mcounter/BatteryCounter/micro/BattRX/UserInterfaceLang.h

#ifndef __USERINTERFACELANG_H_
#define __USERINTERFACELANG_H_

#define USER_TEXT_CONST_EMPTY                                           (0)
#define USER_TEXT_CONST_MESSAGE_DONE                                    (1)
#define USER_TEXT_CONST_MESSAGE_ERROR                                   (2)
#define USER_TEXT_CONST_MESSAGE_SAVING                                  (3)
#define USER_TEXT_CONST_SWITCH_OFF                                      (4)
#define USER_TEXT_CONST_SWITCH_ON                                       (5)
#define USER_TEXT_CONST_SWITCH_NO                                       (6)
#define USER_TEXT_CONST_SWITCH_YES                                      (7)
#define USER_TEXT_CONST_MENU_REPORTS                                    (8)
#define USER_TEXT_CONST_MENU_SETUP                                      (9)
#define USER_TEXT_CONST_MENU_MAINTENANCE                                (10)
#define USER_TEXT_CONST_MENU_INFO                                       (11)
#define USER_TEXT_CONST_SETUP_CLOCK                                     (12)
#define USER_TEXT_CONST_SETUP_SUMMERTIME_L1                             (13)
#define USER_TEXT_CONST_SETUP_SUMMERTIME_L2                             (14)
#define USER_TEXT_CONST_SETUP_SUMMERTIME_AUTO                           (15)
#define USER_TEXT_CONST_SETUP_SUMMERTIME_UKR                            (16)
#define USER_TEXT_CONST_SETUP_COUNTER_L1                                (17)
#define USER_TEXT_CONST_SETUP_COUNTER_L2                                (18)
#define USER_TEXT_CONST_SETUP_COUNTER_DETECTOR_L1                       (19)
#define USER_TEXT_CONST_SETUP_COUNTER_DETECTOR_L2                       (20)
#define USER_TEXT_CONST_SETUP_COUNTER_DETECTOR_NODETECTION              (21)
#define USER_TEXT_CONST_SETUP_COUNTER_DETECTOR_NODETECTIONDIV2          (22)
#define USER_TEXT_CONST_SETUP_COUNTER_DETECTOR_SIMULATION               (23)
#define USER_TEXT_CONST_SETUP_COUNTER_DETECTOR_STRONGDETECTION          (24)
#define USER_TEXT_CONST_SETUP_COUNTER_DETECTOR_SOFTDETECTION            (25)
#define USER_TEXT_CONST_SETUP_COUNTER_INVERTCOUNT_L1                    (26)
#define USER_TEXT_CONST_SETUP_COUNTER_INVERTCOUNT_L2                    (27)
#define USER_TEXT_CONST_SETUP_COUNTER_DETECTIONTIME                     (28)
#define USER_TEXT_CONST_SETUP_ENERGYSAVING_L1                           (29)
#define USER_TEXT_CONST_SETUP_ENERGYSAVING_L2                           (30)
#define USER_TEXT_CONST_SETUP_ENERGYSAVING_SAVEMODE_L1                  (31)
#define USER_TEXT_CONST_SETUP_ENERGYSAVING_SAVEMODE_L2                  (32)
#define USER_TEXT_CONST_SETUP_ENERGYSAVING_SAVEMODE_MIN                 (33)
#define USER_TEXT_CONST_SETUP_ENERGYSAVING_SAVEMODE_NOCOUNT_L1          (34)
#define USER_TEXT_CONST_SETUP_ENERGYSAVING_SAVEMODE_NOCOUNT_L2          (35)
#define USER_TEXT_CONST_SETUP_ENERGYSAVING_SAVEMODE_NOSCREEN_L1         (36)
#define USER_TEXT_CONST_SETUP_ENERGYSAVING_SAVEMODE_NOSCREEN_L2         (37)
#define USER_TEXT_CONST_SETUP_ENERGYSAVING_SAVEMODE_MAX                 (38)
#define USER_TEXT_CONST_SETUP_ENERGYSAVING_INACTIVITYTIME_L1            (39)
#define USER_TEXT_CONST_SETUP_ENERGYSAVING_INACTIVITYTIME_L2            (40)
#define USER_TEXT_CONST_SETUP_ENERGYSAVING_WORKWEEK_L1                  (41)
#define USER_TEXT_CONST_SETUP_ENERGYSAVING_WORKWEEK_L2                  (42)
#define USER_TEXT_CONST_SETUP_ENERGYSAVING_WORKWEEK_MASK                (43)
#define USER_TEXT_CONST_SETUP_ENERGYSAVING_WORKTODAY_L1                 (44)
#define USER_TEXT_CONST_SETUP_ENERGYSAVING_WORKTODAY_L2                 (45)
#define USER_TEXT_CONST_SETUP_ENERGYSAVING_WORKDAY_L1                   (46)
#define USER_TEXT_CONST_SETUP_ENERGYSAVING_WORKDAY_L2                   (47)
#define USER_TEXT_CONST_SETUP_ENERGYSAVING_WORKDAY_24H                  (48)
#define USER_TEXT_CONST_SETUP_ENERGYSAVING_WORKDAY_1SHIFT               (49)
#define USER_TEXT_CONST_SETUP_ENERGYSAVING_WORKDAY_2SHIFTS              (50)
#define USER_TEXT_CONST_SETUP_ENERGYSAVING_WORKDAY_WITHLUNCH            (51)
#define USER_TEXT_CONST_SETUP_PASSWORD                                  (52)
#define USER_TEXT_CONST_SETUP_PASSWORD_MASTER                           (53)
#define USER_TEXT_CONST_SETUP_PASSWORD_MANAGER                          (54)
#define USER_TEXT_CONST_SETUP_PASSWORD_CURRENT                          (55)
#define USER_TEXT_CONST_SETUP_PASSWORD_NEW                              (56)
#define USER_TEXT_CONST_SETUP_PASSWORD_REPEAT                           (57)
#define USER_TEXT_CONST_SETUP_INTERFACE                                 (58)
#define USER_TEXT_CONST_MAINTENANCE_RESET_COUNTERS_L1                   (59)
#define USER_TEXT_CONST_MAINTENANCE_RESET_COUNTERS_L2                   (60)
#define USER_TEXT_CONST_MAINTENANCE_RESET_FACTORY_L1                    (61)
#define USER_TEXT_CONST_MAINTENANCE_RESET_FACTORY_L2                    (62)
#define USER_TEXT_CONST_MAINTENANCE_RESET_DATA                          (63)
#define USER_TEXT_CONST_MAINTENANCE_RESET_FULL                          (64)
#define USER_TEXT_CONST_MAINTENANCE_SAFE_BATT_REMOVE_L1                 (65)
#define USER_TEXT_CONST_MAINTENANCE_SAFE_BATT_REMOVE_L2                 (66)
#define USER_TEXT_CONST_REPORTS_VISITORS                                (67)
#define USER_TEXT_CONST_REPORTS_TOTAL                                   (68)
#define USER_TEXT_CONST_REPORTS_HOUR                                    (69)
#define USER_TEXT_CONST_REPORTS_DAY                                     (70)
#define USER_TEXT_CONST_REPORTS_WEEK                                    (71)
#define USER_TEXT_CONST_REPORTS_MONTH                                   (72)
#define USER_TEXT_CONST_REPORTS_NOSENSOR                                (73)
#define USER_TEXT_CONST_REPORTS_MESSAGE_INCNT                           (74)
#define USER_TEXT_CONST_REPORTS_MESSAGE_OUTCNT                          (75)
#define USER_TEXT_CONST_REPORTS_MESSAGE_TOTALCNT                        (76)
#define USER_TEXT_CONST_REPORTS_MESSAGE_INCNT_SHORT                     (77)
#define USER_TEXT_CONST_REPORTS_MESSAGE_OUTCNT_SHORT                    (78)
#define USER_TEXT_CONST_MONTH_NAME_JANUARY                              (79)
#define USER_TEXT_CONST_MONTH_NAME_FEBRUARY                             (80)
#define USER_TEXT_CONST_MONTH_NAME_MARCH                                (81)
#define USER_TEXT_CONST_MONTH_NAME_APRIL                                (82)
#define USER_TEXT_CONST_MONTH_NAME_MAY                                  (83)
#define USER_TEXT_CONST_MONTH_NAME_JUNE                                 (84)
#define USER_TEXT_CONST_MONTH_NAME_JULY                                 (85)
#define USER_TEXT_CONST_MONTH_NAME_AUGUST                               (86)
#define USER_TEXT_CONST_MONTH_NAME_SEPTEMBER                            (87)
#define USER_TEXT_CONST_MONTH_NAME_OCTOBER                              (88)
#define USER_TEXT_CONST_MONTH_NAME_NOVEMBER                             (89)
#define USER_TEXT_CONST_MONTH_NAME_DECEMBER                             (90)
#define USER_TEXT_CONST_TEXT_MILLISECONDS_SHORT                         (91)
#define USER_TEXT_CONST_TEXT_SECONDS_SHORT                              (92)
#define USER_TEXT_CONST_TEXT_TIMEOUT                                    (93)
#define USER_TEXT_CONST_TEXT_SHIFT1                                     (94)
#define USER_TEXT_CONST_TEXT_SHIFT2                                     (95)
#define USER_TEXT_CONST_TEXT_LUNCH                                      (96)
#define USER_TEXT_CONST_MESSAGE_TYPE_PASSWORD                           (97)
#define USER_TEXT_CONST_TEXT_WIDGET_COUNT_IN                            (98)
#define USER_TEXT_CONST_TEXT_WIDGET_COUNT_OUT                           (99)
#define USER_TEXT_CONST_TEXT_WIDGET_COUNT_AVG                           (100)
#define USER_TEXT_CONST_TEXT_WIDGET_COUNT_MAX                           (101)
#define USER_TEXT_CONST_TEXT_WIDGET_COUNT_MIN                           (102)
#define USER_TEXT_CONST_TEXT_WIDGET_NOSENSOR                            (103)
#define USER_TEXT_CONST_TEXT_WIDGET_HOUR_SHORT                          (104)
#define USER_TEXT_CONST_TEXT_WIDGET_DAY_SHORT                           (105)
#define USER_TEXT_CONST_TEXT_WIDGET_WEEK_SHORT                          (106)
#define USER_TEXT_CONST_TEXT_WIDGET_MONTH_SHORT                         (107)
#define USER_TEXT_CONST_TEXT_WIDGET_TOTAL_SHORT                         (108)
#define USER_TEXT_CONST_INFO_RESETNUM_L1                                (109)
#define USER_TEXT_CONST_INFO_RESETNUM_L2                                (110)
#define USER_TEXT_CONST_INFO_RESETNUM_RESTARTS                          (111)
#define USER_TEXT_CONST_INFO_RESETNUM_DATARESET                         (112)
#define USER_TEXT_CONST_INFO_RESETNUM_FACTORYRESET                      (113)
#define USER_TEXT_CONST_INFO_RESETNUM_PASSWORDFAILS_L1                  (114)
#define USER_TEXT_CONST_INFO_RESETNUM_PASSWORDFAILS_L2                  (115)
#define USER_TEXT_CONST_INFO_SERIALNUM                                  (116)
#define USER_TEXT_CONST_INFO_BATTERY_VOLTAGE                            (117)
#define USER_TEXT_CONST_MAINTENANCE_SENSORQUALITY_L1                    (118)
#define USER_TEXT_CONST_MAINTENANCE_SENSORQUALITY_L2                    (119)
#define USER_TEXT_CONST_SETUP_ENERGYSAVING_BACKLIGHT                    (120)
#define USER_TEXT_CONST_SETUP_WIDGETS                                   (121)
#define USER_TEXT_CONST_SETUP_WIDGETS_L1                                (122)
#define USER_TEXT_CONST_SETUP_WIDGETS_MAIN                              (123)
#define USER_TEXT_CONST_SETUP_WIDGETS_LEFT                              (124)
#define USER_TEXT_CONST_SETUP_WIDGETS_RIGHT                             (125)
#define USER_TEXT_CONST_TEXT_WIDGET_SWITCHED_OFF                        (126)
#define USER_TEXT_CONST_TEXT_WIDGET_COUNTER1_SHORT                      (127)
#define USER_TEXT_CONST_TEXT_WIDGET_COUNTER2_SHORT                      (128)
#define USER_TEXT_CONST_TEXT_WIDGET_COUNTER1_LONG                       (129)
#define USER_TEXT_CONST_TEXT_WIDGET_COUNTER2_LONG                       (130)
#define USER_TEXT_CONST_TEXT_WIDGET_COUNTER_AGGREGATION_MODE            (131)
#define USER_TEXT_CONST_TEXT_WIDGET_COUNTER_AGGREGATION_IN              (132)
#define USER_TEXT_CONST_TEXT_WIDGET_COUNTER_AGGREGATION_OUT             (133)
#define USER_TEXT_CONST_TEXT_WIDGET_COUNTER_AGGREGATION_AVG             (134)
#define USER_TEXT_CONST_TEXT_WIDGET_COUNTER_AGGREGATION_MAX             (135)
#define USER_TEXT_CONST_TEXT_WIDGET_COUNTER_AGGREGATION_MIN             (136)
#define USER_TEXT_CONST_TEXT_WIDGET_COUNTER_SHIFT                       (137)
#define USER_TEXT_CONST_SETUP_SCREENSAVER                               (138)
#define USER_TEXT_CONST_SETUP_SCREENSAVER_OFF                           (139)
#define USER_TEXT_CONST_SETUP_SCREENSAVER_ON                            (140)

namespace UserInterface
{
  unsigned char __generic * getString(unsigned short _strId);
}
#endif
