mcounter/BatteryCounter/micro/BattRX/UserInterfaceLang_RUS.h

#ifndef __USERINTERFACELANG_RUS_H_
#define __USERINTERFACELANG_RUS_H_

namespace UserInterface
{
  __flash const unsigned short textReference_RUS[] =
  {
       0,         //USER_TEXT_CONST_EMPTY
       1,         //USER_TEXT_CONST_MESSAGE_DONE
      11,         //USER_TEXT_CONST_MESSAGE_ERROR
      18,         //USER_TEXT_CONST_MESSAGE_SAVING
      29,         //USER_TEXT_CONST_SWITCH_OFF
      39,         //USER_TEXT_CONST_SWITCH_ON
      48,         //USER_TEXT_CONST_SWITCH_NO
      52,         //USER_TEXT_CONST_SWITCH_YES
      55,         //USER_TEXT_CONST_MENU_REPORTS
      62,         //USER_TEXT_CONST_MENU_SETUP
      72,         //USER_TEXT_CONST_MENU_MAINTENANCE
      85,         //USER_TEXT_CONST_MENU_INFO
      96,         //USER_TEXT_CONST_SETUP_CLOCK
     109,         //USER_TEXT_CONST_SETUP_SUMMERTIME_L1
     116,         //USER_TEXT_CONST_SETUP_SUMMERTIME_L2
     122,         //USER_TEXT_CONST_SETUP_SUMMERTIME_AUTO
     136,         //USER_TEXT_CONST_SETUP_SUMMERTIME_UKR
     144,         //USER_TEXT_CONST_SETUP_COUNTER_L1
     152,         //USER_TEXT_CONST_SETUP_COUNTER_L2
     164,         //USER_TEXT_CONST_SETUP_COUNTER_DETECTOR_L1
     173,         //USER_TEXT_CONST_SETUP_COUNTER_DETECTOR_L2
     185,         //USER_TEXT_CONST_SETUP_COUNTER_DETECTOR_NODETECTION
     198,         //USER_TEXT_CONST_SETUP_COUNTER_DETECTOR_NODETECTIONDIV2
     210,         //USER_TEXT_CONST_SETUP_COUNTER_DETECTOR_SIMULATION
     219,         //USER_TEXT_CONST_SETUP_COUNTER_DETECTOR_STRONGDETECTION
     235,         //USER_TEXT_CONST_SETUP_COUNTER_DETECTOR_SOFTDETECTION
     251,         //USER_TEXT_CONST_SETUP_COUNTER_INVERTCOUNT_L1
     265,         //USER_TEXT_CONST_SETUP_COUNTER_INVERTCOUNT_L2
     270,         //USER_TEXT_CONST_SETUP_COUNTER_DETECTIONTIME
     285,         //USER_TEXT_CONST_SETUP_ENERGYSAVING_L1
     294,         //USER_TEXT_CONST_SETUP_ENERGYSAVING_L2
     302,         //USER_TEXT_CONST_SETUP_ENERGYSAVING_SAVEMODE_L1
     308,         //USER_TEXT_CONST_SETUP_ENERGYSAVING_SAVEMODE_L2
     317,         //USER_TEXT_CONST_SETUP_ENERGYSAVING_SAVEMODE_MIN
     325,         //USER_TEXT_CONST_SETUP_ENERGYSAVING_SAVEMODE_NOCOUNT_L1
     336,         //USER_TEXT_CONST_SETUP_ENERGYSAVING_SAVEMODE_NOCOUNT_L2
     343,         //USER_TEXT_CONST_SETUP_ENERGYSAVING_SAVEMODE_NOSCREEN_L1
     353,         //USER_TEXT_CONST_SETUP_ENERGYSAVING_SAVEMODE_NOSCREEN_L2
     359,         //USER_TEXT_CONST_SETUP_ENERGYSAVING_SAVEMODE_MAX
     368,         //USER_TEXT_CONST_SETUP_ENERGYSAVING_INACTIVITYTIME_L1
     375,         //USER_TEXT_CONST_SETUP_ENERGYSAVING_INACTIVITYTIME_L2
     387,         //USER_TEXT_CONST_SETUP_ENERGYSAVING_WORKWEEK_L1
     395,         //USER_TEXT_CONST_SETUP_ENERGYSAVING_WORKWEEK_L2
     402,         //USER_TEXT_CONST_SETUP_ENERGYSAVING_WORKWEEK_MASK
     416,         //USER_TEXT_CONST_SETUP_ENERGYSAVING_WORKTODAY_L1
     425,         //USER_TEXT_CONST_SETUP_ENERGYSAVING_WORKTODAY_L2
     433,         //USER_TEXT_CONST_SETUP_ENERGYSAVING_WORKDAY_L1
     441,         //USER_TEXT_CONST_SETUP_ENERGYSAVING_WORKDAY_L2
     446,         //USER_TEXT_CONST_SETUP_ENERGYSAVING_WORKDAY_24H
     454,         //USER_TEXT_CONST_SETUP_ENERGYSAVING_WORKDAY_1SHIFT
     462,         //USER_TEXT_CONST_SETUP_ENERGYSAVING_WORKDAY_2SHIFTS
     470,         //USER_TEXT_CONST_SETUP_ENERGYSAVING_WORKDAY_WITHLUNCH
     482,         //USER_TEXT_CONST_SETUP_PASSWORD
     489,         //USER_TEXT_CONST_SETUP_PASSWORD_MASTER
     504,         //USER_TEXT_CONST_SETUP_PASSWORD_MANAGER
     514,         //USER_TEXT_CONST_SETUP_PASSWORD_CURRENT
     529,         //USER_TEXT_CONST_SETUP_PASSWORD_NEW
     542,         //USER_TEXT_CONST_SETUP_PASSWORD_REPEAT
     552,         //USER_TEXT_CONST_SETUP_INTERFACE
     562,         //USER_TEXT_CONST_MAINTENANCE_RESET_COUNTERS_L1
     568,         //USER_TEXT_CONST_MAINTENANCE_RESET_COUNTERS_L2
     578,         //USER_TEXT_CONST_MAINTENANCE_RESET_FACTORY_L1
     588,         //USER_TEXT_CONST_MAINTENANCE_RESET_FACTORY_L2
     598,         //USER_TEXT_CONST_MAINTENANCE_RESET_DATA
     613,         //USER_TEXT_CONST_MAINTENANCE_RESET_FULL
     626,         //USER_TEXT_CONST_MAINTENANCE_SAFE_BATT_REMOVE_L1
     637,         //USER_TEXT_CONST_MAINTENANCE_SAFE_BATT_REMOVE_L2
     645,         //USER_TEXT_CONST_REPORTS_VISITORS
     656,         //USER_TEXT_CONST_REPORTS_TOTAL
     665,         //USER_TEXT_CONST_REPORTS_HOUR
     672,         //USER_TEXT_CONST_REPORTS_DAY
     680,         //USER_TEXT_CONST_REPORTS_WEEK
     690,         //USER_TEXT_CONST_REPORTS_MONTH
     699,         //USER_TEXT_CONST_REPORTS_NOSENSOR
     710,         //USER_TEXT_CONST_REPORTS_MESSAGE_INCNT
     717,         //USER_TEXT_CONST_REPORTS_MESSAGE_OUTCNT
     724,         //USER_TEXT_CONST_REPORTS_MESSAGE_TOTALCNT
     731,         //USER_TEXT_CONST_REPORTS_MESSAGE_INCNT_SHORT
     734,         //USER_TEXT_CONST_REPORTS_MESSAGE_OUTCNT_SHORT
     738,         //USER_TEXT_CONST_MONTH_NAME_JANUARY
     745,         //USER_TEXT_CONST_MONTH_NAME_FEBRUARY
     753,         //USER_TEXT_CONST_MONTH_NAME_MARCH
     758,         //USER_TEXT_CONST_MONTH_NAME_APRIL
     765,         //USER_TEXT_CONST_MONTH_NAME_MAY
     769,         //USER_TEXT_CONST_MONTH_NAME_JUNE
     774,         //USER_TEXT_CONST_MONTH_NAME_JULY
     779,         //USER_TEXT_CONST_MONTH_NAME_AUGUST
     786,         //USER_TEXT_CONST_MONTH_NAME_SEPTEMBER
     795,         //USER_TEXT_CONST_MONTH_NAME_OCTOBER
     803,         //USER_TEXT_CONST_MONTH_NAME_NOVEMBER
     810,         //USER_TEXT_CONST_MONTH_NAME_DECEMBER
     818,         //USER_TEXT_CONST_TEXT_MILLISECONDS_SHORT
     821,         //USER_TEXT_CONST_TEXT_SECONDS_SHORT
     825,         //USER_TEXT_CONST_TEXT_TIMEOUT
     833,         //USER_TEXT_CONST_TEXT_SHIFT1
     841,         //USER_TEXT_CONST_TEXT_SHIFT2
     849,         //USER_TEXT_CONST_TEXT_LUNCH
     854,         //USER_TEXT_CONST_MESSAGE_TYPE_PASSWORD
     869,         //USER_TEXT_CONST_TEXT_WIDGET_COUNT_IN
     872,         //USER_TEXT_CONST_TEXT_WIDGET_COUNT_OUT
     876,         //USER_TEXT_CONST_TEXT_WIDGET_COUNT_AVG
     879,         //USER_TEXT_CONST_TEXT_WIDGET_COUNT_MAX
     883,         //USER_TEXT_CONST_TEXT_WIDGET_COUNT_MIN
     887,         //USER_TEXT_CONST_TEXT_WIDGET_NOSENSOR
     891,         //USER_TEXT_CONST_TEXT_WIDGET_HOUR_SHORT
     893,         //USER_TEXT_CONST_TEXT_WIDGET_DAY_SHORT
     895,         //USER_TEXT_CONST_TEXT_WIDGET_WEEK_SHORT
     897,         //USER_TEXT_CONST_TEXT_WIDGET_MONTH_SHORT
     899,         //USER_TEXT_CONST_TEXT_WIDGET_TOTAL_SHORT
     901,         //USER_TEXT_CONST_INFO_RESETNUM_L1
     912,         //USER_TEXT_CONST_INFO_RESETNUM_L2
     920,         //USER_TEXT_CONST_INFO_RESETNUM_RESTARTS
     933,         //USER_TEXT_CONST_INFO_RESETNUM_DATARESET
     946,         //USER_TEXT_CONST_INFO_RESETNUM_FACTORYRESET
     961,         //USER_TEXT_CONST_INFO_RESETNUM_PASSWORDFAILS_L1
     969,         //USER_TEXT_CONST_INFO_RESETNUM_PASSWORDFAILS_L2
     982,         //USER_TEXT_CONST_INFO_SERIALNUM
     997,         //USER_TEXT_CONST_INFO_BATTERY_VOLTAGE
    1011,         //USER_TEXT_CONST_MAINTENANCE_SENSORQUALITY_L1
    1023,         //USER_TEXT_CONST_MAINTENANCE_SENSORQUALITY_L2
    1032,         //USER_TEXT_CONST_SETUP_ENERGYSAVING_BACKLIGHT
    1042,         //USER_TEXT_CONST_SETUP_WIDGETS
    1050,         //USER_TEXT_CONST_SETUP_WIDGETS_L1
    1057,         //USER_TEXT_CONST_SETUP_WIDGETS_MAIN
    1066,         //USER_TEXT_CONST_SETUP_WIDGETS_LEFT
    1072,         //USER_TEXT_CONST_SETUP_WIDGETS_RIGHT
    1079,         //USER_TEXT_CONST_TEXT_WIDGET_SWITCHED_OFF
    1090,         //USER_TEXT_CONST_TEXT_WIDGET_COUNTER1_SHORT
    1095,         //USER_TEXT_CONST_TEXT_WIDGET_COUNTER2_SHORT
    1100,         //USER_TEXT_CONST_TEXT_WIDGET_COUNTER1_LONG
    1110,         //USER_TEXT_CONST_TEXT_WIDGET_COUNTER2_LONG
    1120,         //USER_TEXT_CONST_TEXT_WIDGET_COUNTER_AGGREGATION_MODE
    1131,         //USER_TEXT_CONST_TEXT_WIDGET_COUNTER_AGGREGATION_IN
    1140,         //USER_TEXT_CONST_TEXT_WIDGET_COUNTER_AGGREGATION_OUT
    1150,         //USER_TEXT_CONST_TEXT_WIDGET_COUNTER_AGGREGATION_AVG
    1158,         //USER_TEXT_CONST_TEXT_WIDGET_COUNTER_AGGREGATION_MAX
    1167,         //USER_TEXT_CONST_TEXT_WIDGET_COUNTER_AGGREGATION_MIN
    1175,         //USER_TEXT_CONST_TEXT_WIDGET_COUNTER_SHIFT
    1182,         //USER_TEXT_CONST_SETUP_SCREENSAVER
    1191,         //USER_TEXT_CONST_SETUP_SCREENSAVER_OFF
    1201,         //USER_TEXT_CONST_SETUP_SCREENSAVER_ON
  };

  __flash const unsigned char textStrings_RUS[] =
  {
     0,                                                                                                           //   0 - 
     9, 0x42, 0xAE, 0xA8, 0x4F, 0xA7, 0x48, 0x45, 0x48, 0x4F,                                                     //   1 - ВЫПОЛНЕНО
     6, 0x4F, 0xAC, 0xA5, 0xA0, 0x4B, 0x41,                                                                       //  11 - ОШИБКА
    10, 0x43, 0x4F, 0x58, 0x50, 0x41, 0x48, 0x45, 0x48, 0xA5, 0x45,                                               //  18 - СОХРАНЕНИЕ
     9, 0x42, 0xC3, 0xBA, 0xBB, 0xC6, 0xC0, 0x65, 0xBD, 0x6F,                                                     //  29 - Выключено
     8, 0x42, 0xBA, 0xBB, 0xC6, 0xC0, 0x65, 0xBD, 0x6F,                                                           //  39 - Включено
     3, 0x48, 0x45, 0x54,                                                                                         //  48 - НЕТ
     2, 0xE0, 0x41,                                                                                               //  52 - ДА
     6, 0x4F, 0xBF, 0xC0, 0x65, 0xBF, 0xC3,                                                                       //  55 - Отчеты
     9, 0x48, 0x61, 0x63, 0xBF, 0x70, 0x6F, 0xB9, 0xBA, 0xB8,                                                     //  62 - Настройки
    12, 0x4F, 0xB2, 0x63, 0xBB, 0x79, 0xB6, 0xB8, 0xB3, 0x61, 0xBD, 0xB8, 0x65,                                   //  72 - Обслуживание
    10, 0xA5, 0xBD, 0xE4, 0x6F, 0x70, 0xBC, 0x61, 0xE5, 0xB8, 0xC7,                                               //  85 - Информация
    12, 0xE0, 0x61, 0xBF, 0x61, 0x20, 0xB8, 0x20, 0xB3, 0x70, 0x65, 0xBC, 0xC7,                                   //  96 - Дата и время
     6, 0xA7, 0x65, 0xBF, 0xBD, 0x65, 0x65,                                                                       // 109 - Летнее
     5, 0xB3, 0x70, 0x65, 0xBC, 0xC7,                                                                             // 116 - время
    13, 0x41, 0xB3, 0xBF, 0x6F, 0xBC, 0x61, 0xBF, 0xB8, 0xC0, 0x65, 0x63, 0xBA, 0xB8,                             // 122 - Автоматически
     7, 0xA9, 0xBA, 0x70, 0x61, 0xB8, 0xBD, 0x61,                                                                 // 136 - Украина
     7, 0xA8, 0x6F, 0xE3, 0x63, 0xC0, 0x65, 0xBF,                                                                 // 144 - Подсчет
    11, 0xBE, 0x6F, 0x63, 0x65, 0xBF, 0xB8, 0xBF, 0x65, 0xBB, 0x65, 0xB9,                                         // 152 - посетителей
     8, 0xE0, 0x65, 0xBF, 0x65, 0xBA, 0xE5, 0xB8, 0xC7,                                                           // 164 - Детекция
    11, 0xBD, 0x61, 0xBE, 0x70, 0x61, 0xB3, 0xBB, 0x65, 0xBD, 0xB8, 0xC7,                                         // 173 - направления
    12, 0xA0, 0x65, 0xB7, 0x20, 0xE3, 0x65, 0xBF, 0x65, 0xBA, 0xE5, 0xB8, 0xB8,                                   // 185 - Без детекции
    11, 0xE0, 0x65, 0xBB, 0xB8, 0xBF, 0xC4, 0x20, 0xBD, 0x61, 0x20, 0x32,                                         // 198 - Делить на 2
     8, 0xA5, 0xBC, 0xB8, 0xBF, 0x61, 0xE5, 0xB8, 0xC7,                                                           // 210 - Имитация
    15, 0xA8, 0x6F, 0xBB, 0xBD, 0x61, 0xC7, 0x20, 0xE3, 0x65, 0xBF, 0x65, 0xBA, 0xE5, 0xB8, 0xC7,                 // 219 - Полная детекция
    15, 0x43, 0xBC, 0x65, 0xC1, 0x61, 0xBD, 0xBD, 0xC3, 0xB9, 0x20, 0x70, 0x65, 0xB6, 0xB8, 0xBC,                 // 235 - Смешанный режим
    13, 0xA5, 0xBD, 0xB3, 0x65, 0x70, 0xBF, 0xB8, 0x70, 0x6F, 0xB3, 0x61, 0xBF, 0xC4,                             // 251 - Инвертировать
     4, 0x63, 0xC0, 0x65, 0xBF,                                                                                   // 265 - счет
    14, 0x42, 0x70, 0x65, 0xBC, 0xC7, 0x20, 0xE3, 0x65, 0xBF, 0x65, 0xBA, 0xE5, 0xB8, 0xB8,                       // 270 - Время детекции
     8, 0xAF, 0xBA, 0x6F, 0xBD, 0x6F, 0xBC, 0xB8, 0xC7,                                                           // 285 - Экономия
     7, 0xC5, 0xBD, 0x65, 0x70, 0xB4, 0xB8, 0xB8,                                                                 // 294 - энергии
     5, 0x50, 0x65, 0xB6, 0xB8, 0xBC,                                                                             // 302 - Режим
     8, 0xC5, 0xBA, 0x6F, 0xBD, 0x6F, 0xBC, 0xB8, 0xB8,                                                           // 308 - экономии
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
     8, 0xB3, 0x78, 0x6F, 0xE3, 0xC7, 0xE6, 0xB8, 0x65,                                                           //1131 - входящие
     9, 0xB3, 0xC3, 0x78, 0x6F, 0xE3, 0xC7, 0xE6, 0xB8, 0x65,                                                     //1140 - выходящие
     7, 0x63, 0x70, 0x65, 0xE3, 0xBD, 0x65, 0x65,                                                                 //1150 - среднее
     8, 0xBC, 0x61, 0xBA, 0x63, 0xB8, 0xBC, 0x79, 0xBC,                                                           //1158 - максимум
     7, 0xBC, 0xB8, 0xBD, 0xB8, 0xBC, 0x79, 0xBC,                                                                 //1167 - минимум
     6, 0x43, 0xE3, 0xB3, 0xB8, 0xB4, 0x3A,                                                                       //1175 - Сдвиг:
     8, 0xA4, 0x61, 0x63, 0xBF, 0x61, 0xB3, 0xBA, 0x61,                                                           //1182 - Заставка
     9, 0xB3, 0xC3, 0xBA, 0xBB, 0xC6, 0xC0, 0x65, 0xBD, 0x61,                                                     //1191 - выключена
    11, 0x63, 0xBF, 0x61, 0xBD, 0xE3, 0x61, 0x70, 0xBF, 0xBD, 0x61, 0xC7,                                         //1201 - стандартная
  };
}

#endif
