mcounter/BatteryCounter/micro/BattRX/GlobalSpace.h

#ifndef __GLOBALSPACE_H_
#define __GLOBALSPACE_H_

#include <ioavr.h>
#include <intrinsics.h>
#include <string.h>
#include <pgmspace.h>

#include "CommonFunctions.h"
#include "GlobalDefinitions.h"
#include "GlobalDeviceProfile.h"

#endif
